JanJanPlay/TI-EtherCAT/EMIF/Src/TMDSECATCNCD379D-EchoBack.h

/**
 * \addtogroup TMDSECATCNCD379D-EchoBack TMDSECATCNCD379D-EchoBack
 * @{
 */

/**
\file TMDSECATCNCD379D-EchoBack.h
\brief TMDSECATCNCD379D-EchoBack function prototypes and defines

\version 1.0.0.11
 */

 
 #ifndef _TMDSECATCNCD379_D_ECHO_BACK_H_
#define _TMDSECATCNCD379_D_ECHO_BACK_H_


/*-----------------------------------------------------------------------------------------
------
------    Includes
------
-----------------------------------------------------------------------------------------*/
#include "ecat_def.h"

#include "ecatappl.h"

/*-----------------------------------------------------------------------------------------
------
------    Defines and Types
------
-----------------------------------------------------------------------------------------*/

#endif //_TMDSECATCNCD379_D_ECHO_BACK_H_

//include custom application object dictionary 
#include "TMDSECATCNCD379D-EchoBackObjects.h"


#if defined(_TMDSECATCNCD379_D_ECHO_BACK_) && (_TMDSECATCNCD379_D_ECHO_BACK_ == 1)
    #define PROTO
#else
    #define PROTO extern
#endif


PROTO void APPL_Application(void);
#if EXPLICIT_DEVICE_ID
PROTO UINT16 APPL_GetDeviceID(void);
#endif

PROTO void   APPL_AckErrorInd(UINT16 stateTrans);
PROTO UINT16 APPL_StartMailboxHandler(void);
PROTO UINT16 APPL_StopMailboxHandler(void);
PROTO UINT16 APPL_StartInputHandler(UINT16 *pIntMask);
PROTO UINT16 APPL_StopInputHandler(void);
PROTO UINT16 APPL_StartOutputHandler(void);
PROTO UINT16 APPL_StopOutputHandler(void);

PROTO UINT16 APPL_GenerateMapping(UINT16 *pInputSize,UINT16 *pOutputSize);
PROTO void APPL_InputMapping(UINT16* pData);
PROTO void APPL_OutputMapping(UINT16* pData);

#undef PROTO
/** @}*/
